Tinkerforge/industrial-analog-out-v2-bricklet/software/src/communication.c

/* industrial-analog-out-v2-bricklet
 * Copyright (C) 2018 Olaf Lüke <olaf@tinkerforge.com>
 * Copyright (C) 2018 Ishraq Ibne Ashraf <ishraq@tinkerforge.com>
 *
 * communication.c: TFP protocol message handling
 *
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
 * You should have received a copy of the GNU Lesser General Public
 * License along with this library; if not, write to the
 * Free Software Foundation, Inc., 59 Temple Place - Suite 330,
 * Boston, MA 02111-1307, USA.
 */

#include "communication.h"

#include "bricklib2/utility/communication_callback.h"
#include "bricklib2/protocols/tfp/tfp.h"

#include "dac7760.h"
#include "bricklib2/utility/util_definitions.h"

BootloaderHandleMessageResponse handle_message(const void *message, void *response) {
	switch(tfp_get_fid_from_message(message)) {
		case FID_SET_ENABLED: return set_enabled(message);
		case FID_GET_ENABLED: return get_enabled(message, response);
		case FID_SET_VOLTAGE: return set_voltage(message);
		case FID_GET_VOLTAGE: return get_voltage(message, response);
		case FID_SET_CURRENT: return set_current(message);
		case FID_GET_CURRENT: return get_current(message, response);
		case FID_SET_CONFIGURATION: return set_configuration(message);
		case FID_GET_CONFIGURATION: return get_configuration(message, response);
		case FID_SET_OUT_LED_CONFIG: return set_out_led_config(message);
		case FID_GET_OUT_LED_CONFIG: return get_out_led_config(message, response);
		case FID_SET_OUT_LED_STATUS_CONFIG: return set_out_led_status_config(message);
		case FID_GET_OUT_LED_STATUS_CONFIG: return get_out_led_status_config(message, response);
		default: return HANDLE_MESSAGE_RESPONSE_NOT_SUPPORTED;
	}
}

BootloaderHandleMessageResponse set_enabled(const SetEnabled *data) {
	dac7760.enabled        = data->enabled;
	dac7760.control_update = true;

	return HANDLE_MESSAGE_RESPONSE_EMPTY;
}

BootloaderHandleMessageResponse get_enabled(const GetEnabled *data, GetEnabled_Response *response) {
	response->header.length = sizeof(GetEnabled_Response);
	response->enabled       = dac7760.enabled;

	return HANDLE_MESSAGE_RESPONSE_NEW_MESSAGE;
}

BootloaderHandleMessageResponse set_voltage(const SetVoltage *data) {
	// Set voltage and value according to data from user
	switch(dac7760.voltage_range) {
		case INDUSTRIAL_ANALOG_OUT_V2_VOLTAGE_RANGE_0_TO_5V: {
			dac7760.voltage = BETWEEN(0, data->voltage, 5000);
			dac7760.value = SCALE(dac7760.voltage, 0, 5000, DAC7760_MIN, DAC7760_MAX);
			break;
		}

		case INDUSTRIAL_ANALOG_OUT_V2_VOLTAGE_RANGE_0_TO_10V: {
			dac7760.voltage = BETWEEN(0, data->voltage, 10000);
			dac7760.value = SCALE(dac7760.voltage, 0, 10000, DAC7760_MIN, DAC7760_MAX);
			break;
		}
	}

	// Update current
	switch(dac7760.current_range) {
		case INDUSTRIAL_ANALOG_OUT_V2_CURRENT_RANGE_4_TO_20MA: {
			dac7760.current = SCALE(dac7760.value, DAC7760_MIN, DAC7760_MAX, 4000, 20000);
			break;
		}

		case INDUSTRIAL_ANALOG_OUT_V2_CURRENT_RANGE_0_TO_20MA: {
			dac7760.current = SCALE(dac7760.value, DAC7760_MIN, DAC7760_MAX, 0, 20000);
			break;
		}

		case INDUSTRIAL_ANALOG_OUT_V2_CURRENT_RANGE_0_TO_24MA: {
			dac7760.current = SCALE(dac7760.value, DAC7760_MIN, DAC7760_MAX, 0, 24000);
			break;
		}
	}

	dac7760.value_update = true;
	dac7760.out_status_led_cfg.out_status_led_show = DAC7760_OUT_STATUS_LED_SHOW_V;

	return HANDLE_MESSAGE_RESPONSE_EMPTY;
}

BootloaderHandleMessageResponse get_voltage(const GetVoltage *data, GetVoltage_Response *response) {
	response->header.length = sizeof(GetVoltage_Response);
	response->voltage       = dac7760.voltage;

	return HANDLE_MESSAGE_RESPONSE_NEW_MESSAGE;
}

BootloaderHandleMessageResponse set_current(const SetCurrent *data) {
	// Set current and value according to data from user
	switch(dac7760.current_range) {
		case INDUSTRIAL_ANALOG_OUT_V2_CURRENT_RANGE_4_TO_20MA: {
			dac7760.current = BETWEEN(4000, data->current, 20000);
			dac7760.value = SCALE(dac7760.current, 4000, 20000, DAC7760_MIN, DAC7760_MAX);
			break;
		}

		case INDUSTRIAL_ANALOG_OUT_V2_CURRENT_RANGE_0_TO_20MA: {
			dac7760.current = BETWEEN(0, data->current, 20000);
			dac7760.value = SCALE(dac7760.current, 0, 20000, DAC7760_MIN, DAC7760_MAX);
			break;
		}

		case INDUSTRIAL_ANALOG_OUT_V2_CURRENT_RANGE_0_TO_24MA: {
			dac7760.current = BETWEEN(0, data->current, 24000);
			dac7760.value = SCALE(dac7760.current, 0, 24000, DAC7760_MIN, DAC7760_MAX);
			break;
		}
	}

	// Update voltage
	switch(dac7760.voltage_range) {
		case INDUSTRIAL_ANALOG_OUT_V2_VOLTAGE_RANGE_0_TO_5V: {
			dac7760.voltage = SCALE(dac7760.value, DAC7760_MIN, DAC7760_MAX, 0, 5000);
			break;
		}

		case INDUSTRIAL_ANALOG_OUT_V2_VOLTAGE_RANGE_0_TO_10V: {
			dac7760.voltage = SCALE(dac7760.value, DAC7760_MIN, DAC7760_MAX, 0, 10000);
			break;
		}
	}

	dac7760.value_update = true;
	dac7760.out_status_led_cfg.out_status_led_show = DAC7760_OUT_STATUS_LED_SHOW_C;

	return HANDLE_MESSAGE_RESPONSE_EMPTY;
}

BootloaderHandleMessageResponse get_current(const GetCurrent *data, GetCurrent_Response *response) {
	response->header.length = sizeof(GetCurrent_Response);
	response->current       = dac7760.current;

	return HANDLE_MESSAGE_RESPONSE_NEW_MESSAGE;
}

BootloaderHandleMessageResponse set_configuration(const SetConfiguration *data) {
	if((data->current_range > INDUSTRIAL_ANALOG_OUT_V2_CURRENT_RANGE_0_TO_24MA) ||
	   (data->voltage_range > INDUSTRIAL_ANALOG_OUT_V2_VOLTAGE_RANGE_0_TO_10V)) {
		return HANDLE_MESSAGE_RESPONSE_INVALID_PARAMETER;
	}

	dac7760.current_range  = data->current_range;
	dac7760.voltage_range  = data->voltage_range;
	dac7760.config_update  = true;
	dac7760.control_update = true;

	return HANDLE_MESSAGE_RESPONSE_EMPTY;
}

BootloaderHandleMessageResponse get_configuration(const GetConfiguration *data, GetConfiguration_Response *response) {
	response->header.length = sizeof(GetConfiguration_Response);
	response->current_range = dac7760.current_range;
	response->voltage_range = dac7760.voltage_range;

	return HANDLE_MESSAGE_RESPONSE_NEW_MESSAGE;
}

BootloaderHandleMessageResponse set_out_led_config(const SetOutLEDConfig *data) {
	dac7760.out_status_led_cfg.config = data->config;

	return HANDLE_MESSAGE_RESPONSE_EMPTY;
}

BootloaderHandleMessageResponse get_out_led_config(const GetOutLEDConfig *data, GetOutLEDConfig_Response *response) {
	response->header.length = sizeof(GetOutLEDConfig_Response);
	response->config = dac7760.out_status_led_cfg.config;

	return HANDLE_MESSAGE_RESPONSE_NEW_MESSAGE;
}

BootloaderHandleMessageResponse set_out_led_status_config(const SetOutLEDStatusConfig *data) {
	if (data->min > 24000 || data->max > 24000) {
		return HANDLE_MESSAGE_RESPONSE_INVALID_PARAMETER;
	}

	if (dac7760.out_status_led_cfg.out_status_led_show == DAC7760_OUT_STATUS_LED_SHOW_V) {
		switch(dac7760.voltage_range) {
			case INDUSTRIAL_ANALOG_OUT_V2_VOLTAGE_RANGE_0_TO_5V: {
				dac7760.out_status_led_cfg.min = BETWEEN(0, data->min, 5000);
				dac7760.out_status_led_cfg.max = BETWEEN(0, data->max, 5000);

				break;
			}

			case INDUSTRIAL_ANALOG_OUT_V2_VOLTAGE_RANGE_0_TO_10V: {
				dac7760.out_status_led_cfg.min = BETWEEN(0, data->min, 10000);
				dac7760.out_status_led_cfg.max = BETWEEN(0, data->max, 10000);

				break;
			}
		}
	}
	else {
		switch(dac7760.current_range) {
			case INDUSTRIAL_ANALOG_OUT_V2_CURRENT_RANGE_4_TO_20MA: {
				dac7760.out_status_led_cfg.min = BETWEEN(4000, data->min, 20000);
				dac7760.out_status_led_cfg.max = BETWEEN(4000, data->max, 20000);

				break;
			}

			case INDUSTRIAL_ANALOG_OUT_V2_CURRENT_RANGE_0_TO_20MA: {
				dac7760.out_status_led_cfg.min = BETWEEN(0, data->min, 20000);
				dac7760.out_status_led_cfg.max = BETWEEN(0, data->max, 20000);

				break;
			}

			case INDUSTRIAL_ANALOG_OUT_V2_CURRENT_RANGE_0_TO_24MA: {
				dac7760.out_status_led_cfg.min = BETWEEN(0, data->min, 24000);
				dac7760.out_status_led_cfg.max = BETWEEN(0, data->max, 24000);

				break;
			}
		}
	}

	dac7760.out_status_led_cfg.config_out_status = data->config;

	return HANDLE_MESSAGE_RESPONSE_EMPTY;
}

BootloaderHandleMessageResponse get_out_led_status_config(const GetOutLEDStatusConfig *data, GetOutLEDStatusConfig_Response *response) {
	response->header.length = sizeof(GetOutLEDStatusConfig_Response);
	response->min = dac7760.out_status_led_cfg.min;
	response->max = dac7760.out_status_led_cfg.max;
	response->config = dac7760.out_status_led_cfg.config_out_status;

	return HANDLE_MESSAGE_RESPONSE_NEW_MESSAGE;
}

void communication_tick(void) {
	communication_callback_tick();
}

void communication_init(void) {
	communication_callback_init();
}
